The-XOR/norns/Barboni!/connessione audio usb.jpg

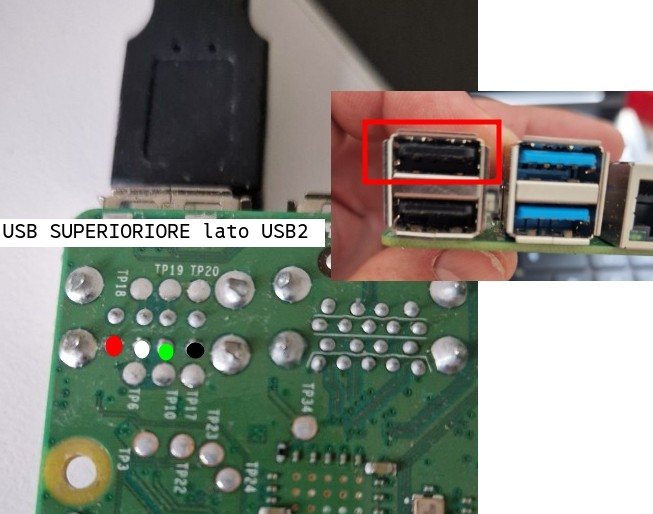
Barboni!/connessione audio usb.jpg
