The-XOR/norns/Barboni!/norns 3.png

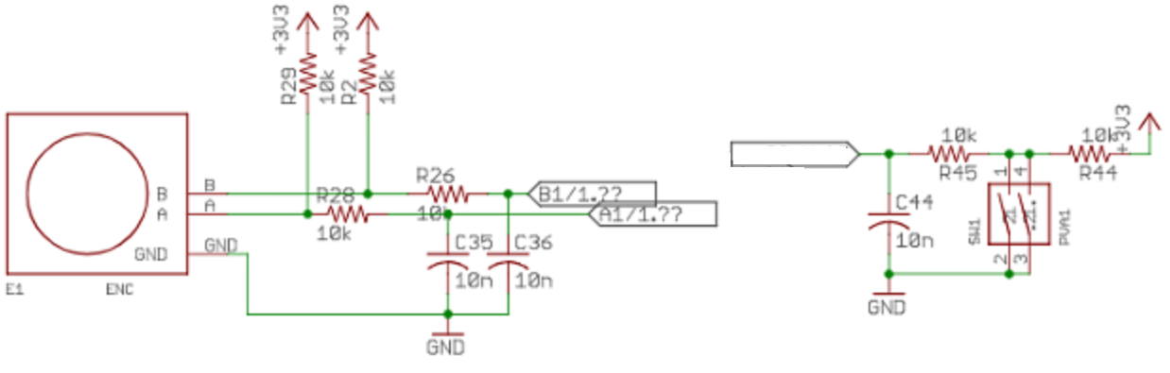
Barboni!/norns 3.png
