The-XOR/norns/Barboni!/norns-2.png

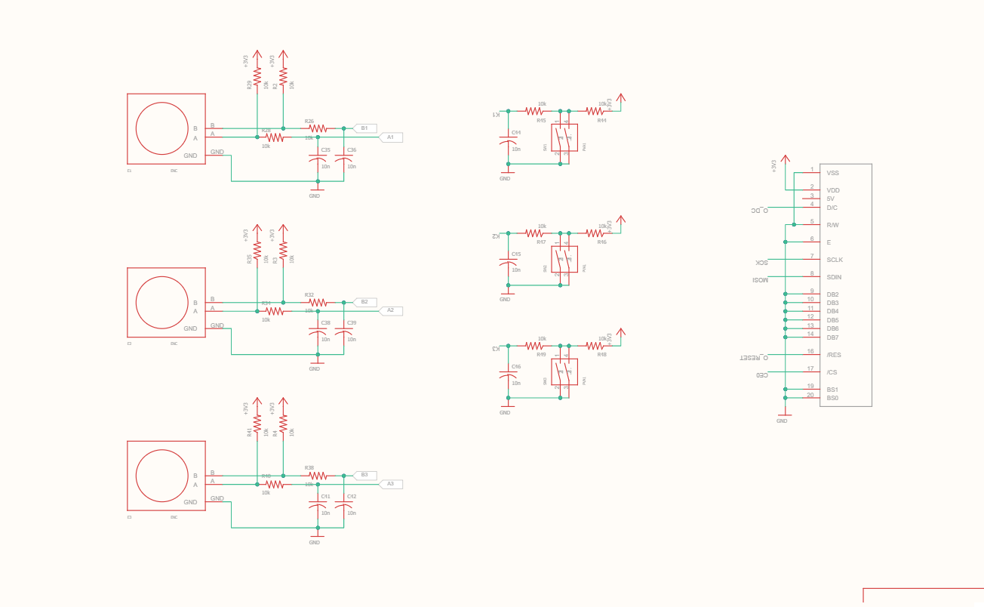
Barboni!/norns-2.png
